oro-os/link/firmware/link-firmware/build.rs

use std::{env, fs, path::Path};

use pixglyph::Glyph;
use proc_macro2::{Span, TokenStream};
use quote::quote;
use syn::{Ident, LitChar, LitInt, punctuated::Punctuated, token::Comma};
use ttf_parser::Face;

const TERM_CHARMAP: &str = "?abcdefghijklmnopqrstuvwxyzABCDEFGHIJKLMNOPQRSTUVWXYZ0123456789!@#$%^&\
                            *()`,.<>/[]-_~'\"=+;:©µ¿\
                            {}ÀÁÂÃÄÅÆÇÈÉÊËÌÍÎÏÐÑÒÓÔÕÖ×ØÙÚÛÜÝÞßàáâãäåæçèéêëìíîïðñòóôõö÷øùúûüýþÿ";
const HEIGHT: f32 = 16.0;
const BASE_TOP: f32 = HEIGHT - 2.0;
const BASE_LEFT: f32 = 1.0;
const THRESHOLD: u8 = 254;

fn render_font(id: &str, path: &str, charmap: &str) -> TokenStream {
	let face_data = fs::read(path).unwrap();
	let face = Face::parse(&face_data[..], 0).unwrap();
	println!("cargo:rerun-if-changed={}", path);

	let mut charmap = charmap.chars().collect::<Vec<_>>();
	charmap.sort();
	let mut char_syn = Punctuated::<LitChar, Comma>::new();
	let mut idx_syn = Punctuated::<LitInt, Comma>::new();
	let mut bytes_syn = Punctuated::<LitInt, Comma>::new();

	for c in charmap {
		char_syn.push(LitChar::new(c, Span::call_site()));
		idx_syn.push(LitInt::new(&bytes_syn.len().to_string(), Span::call_site()));

		let glyph_normal = face
			.glyph_index(c)
			.unwrap_or_else(|| panic!("normal face has no glyph for character {}: {c}", c as u16));

		let glyph = Glyph::load(&face, glyph_normal).unwrap();
		let bmp = glyph.rasterize(BASE_LEFT, BASE_TOP, HEIGHT);

		let total_bytes = (bmp.width * bmp.height).div_ceil(8) as usize;
		let mut bytes = vec![0u8; total_bytes];

		for y in 0..bmp.height {
			for x in 0..bmp.width {
				let index = (y * bmp.width + x) as usize;
				let byte_index = index / 8;
				let shift = index % 8;
				let bitval = ((bmp.coverage[index] >= THRESHOLD) as u8) << shift;
				bytes[byte_index] |= bitval;
			}
		}

		assert!(bmp.width <= 255);
		assert!(bmp.height <= 255);
		assert!(bmp.top <= 255);

		let width = bmp.width as u8;
		let height = bmp.height as u8;
		let top = bmp.top as u8;

		bytes_syn.push(LitInt::new(&top.to_string(), Span::call_site()));
		bytes_syn.push(LitInt::new(&width.to_string(), Span::call_site()));
		bytes_syn.push(LitInt::new(&height.to_string(), Span::call_site()));

		for b in bytes {
			bytes_syn.push(LitInt::new(&b.to_string(), Span::call_site()));
		}
	}

	let id_syn = Ident::new(id, Span::call_site());
	let num_chars = char_syn.len();
	let num_bytes = bytes_syn.len();

	quote! {
		pub struct #id_syn;
		impl FontData for #id_syn {
			#[inline(always)]
			fn charmap() -> &'static [char] {
				const CHARMAP: [char; #num_chars] = [ #char_syn ];
				&CHARMAP[..]
			}

			#[inline(always)]
			fn idxmap() -> &'static [u16] {
				const IDXMAP: [u16; #num_chars] = [ #idx_syn ];
				&IDXMAP[..]
			}

			#[inline(always)]
			fn data() -> &'static [u8] {
				const DATA: [u8; #num_bytes] = [ #bytes_syn ];
				&DATA[..]
			}
		}
	}
}

pub fn main() {
	let out_dir_os = env::var_os("OUT_DIR").unwrap();
	let out_dir = Path::new(&out_dir_os);

	//#[cfg(debug_assertions)]
	// println!("cargo:rustc-env=DEFMT_LOG=trace");
	// println!("cargo:rustc-env=DEFMT_LOG=trace,embassy_net=trace,embassy_hal_internal=warn");
	//#[cfg(not(debug_assertions))]
	// println!("cargo:rustc-env=DEFMT_LOG=warn");

	println!(
		"cargo:rustc-link-arg=-L{}",
		env::var("CARGO_MANIFEST_DIR").unwrap()
	);
	println!("cargo:rustc-link-arg=-Tlink.x");
	println!("cargo:rustc-link-arg=-Tdefmt.x");
	println!(
		"cargo:rerun-if-changed={}/memory.x",
		env::var("CARGO_MANIFEST_DIR").unwrap()
	);
	println!(
		"cargo:rerun-if-changed={}/thumbv7-none-eabihf.json",
		env::var("CARGO_MANIFEST_DIR").unwrap()
	);

	let mut font_source = quote! { use super::FontData; };
	font_source.extend(render_font(
		"TermNormal",
		"../font/EnterCommand.ttf",
		TERM_CHARMAP,
	));
	font_source.extend(render_font(
		"TermBold",
		"../font/EnterCommand-Bold.ttf",
		TERM_CHARMAP,
	));

	let source = font_source.to_string();

	let dest_path = out_dir.join("oro-link-fontdata.rs");
	fs::write(dest_path, source).unwrap();

	std::fs::write(
		out_dir.join("version_info.rs"),
		format!(
			r#"
		pub const VERSION_MAJOR: u64 = {};
		pub const VERSION_MINOR: u64 = {};
		pub const VERSION_PATCH: u64 = {};
		"#,
			env!("CARGO_PKG_VERSION_MAJOR"),
			env!("CARGO_PKG_VERSION_MINOR"),
			env!("CARGO_PKG_VERSION_PATCH"),
		),
	)
	.unwrap();

	println!("cargo:rerun-if-changed=build.rs");
}
